iBelieve/ehymnboard/hardware/render-2024-08-22.png

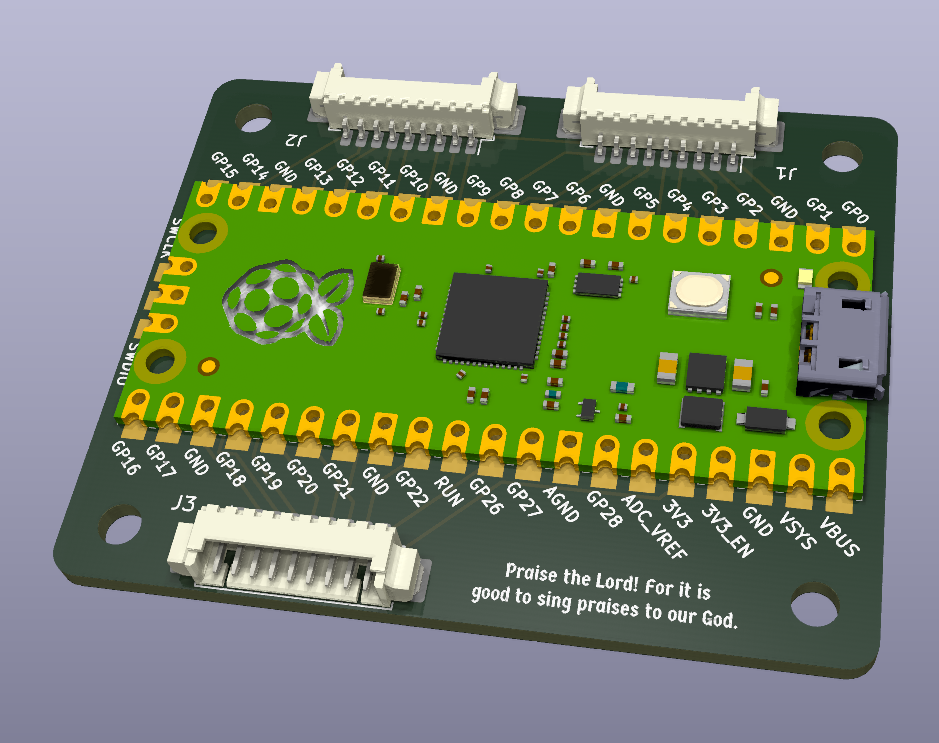
hardware/render-2024-08-22.png
